Nathan-Busse-private/S.P.A.R.K/Src/Scripts/Alpha/Alpha/Stable/Models/Leg parts/Coxae/x4/Coxae joint bracket.stl

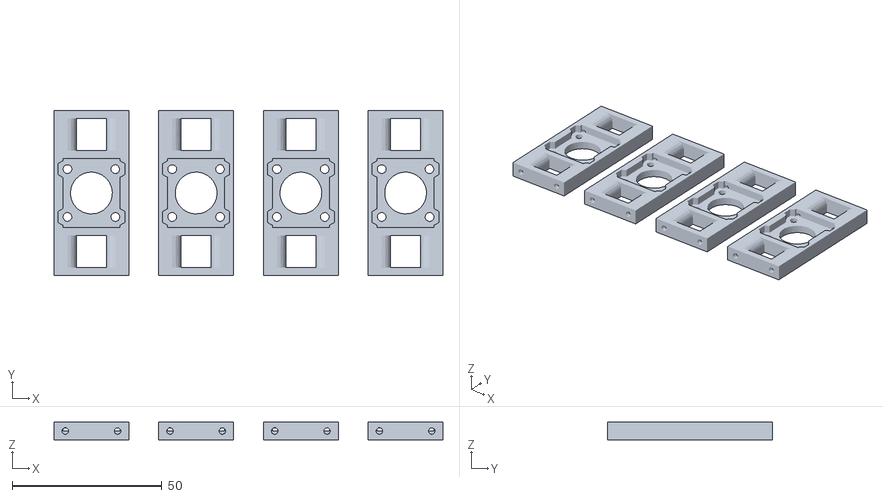
[picture p16: CAD file, 2023-09-16]
Src/Scripts/Alpha/Alpha/Stable/Models/Leg parts/Coxae/x4/Coxae joint bracket.stl
130.0 x 55.2 x 6.00
