Nathan-Busse-private/S.P.A.R.K/Src/Scripts/In-Dev/In-Dev/Stable/Models/Body parts/x1/top.stl

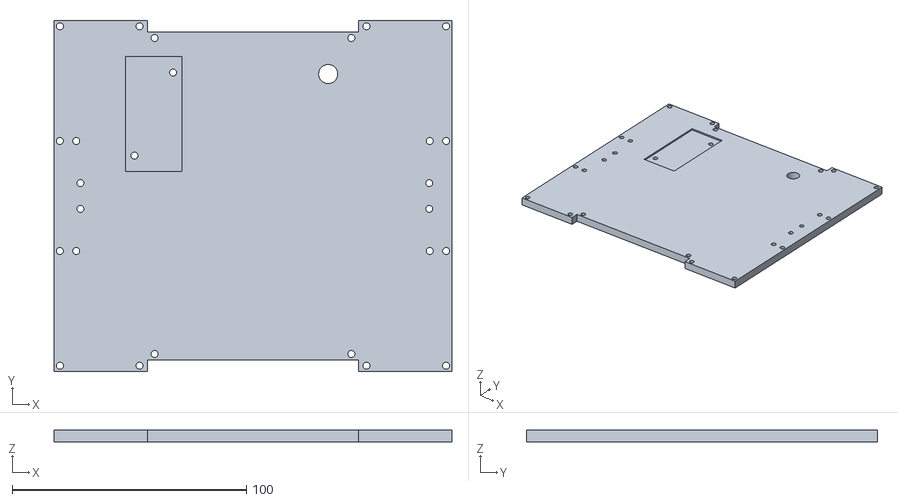
[picture p17: CAD file, 2023-08-11]
Src/Scripts/In-Dev/In-Dev/Stable/Models/Body parts/x1/top.stl
170.0 x 150.0 x 5.00
