Nathan-Busse-private/S.P.A.R.K/Src/Scripts/Alpha/Alpha/Models/Body parts/x1/30mm fan mount.stl

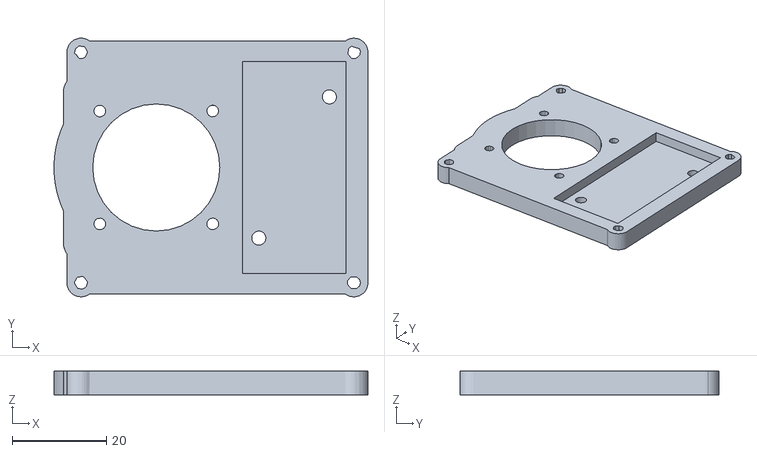
[picture p18: CAD file, 2023-08-11]
Src/Scripts/Alpha/Alpha/Models/Body parts/x1/30mm fan mount.stl
66.7 x 55.0 x 5.00
