Nathan-Busse-private/S.P.A.R.K/Src/Scripts/Alpha/Alpha/Models/Leg parts/Coxae/x4/Coxae joint horn bracket.stl

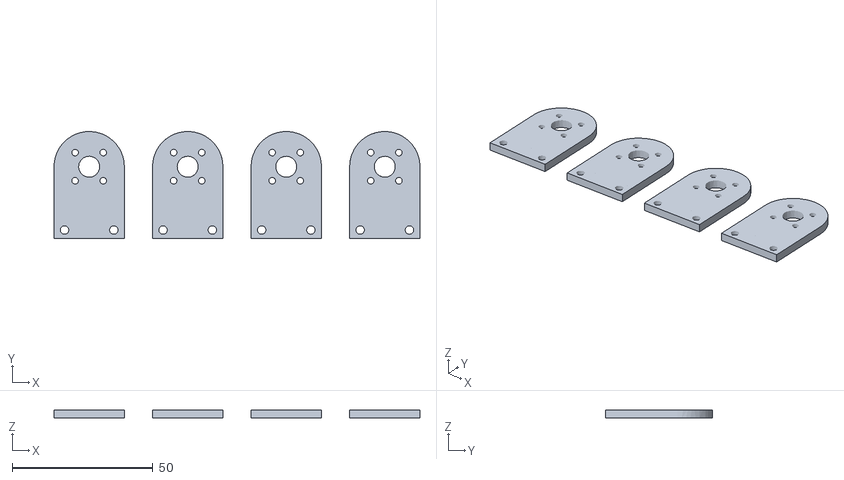
[picture p19: CAD file, 2023-09-16]
Src/Scripts/Alpha/Alpha/Models/Leg parts/Coxae/x4/Coxae joint horn bracket.stl
130.0 x 38.0 x 3.00
