Nathan-Busse-private/S.P.A.R.K/Src/Scripts/Alpha/Alpha/Models/Leg parts/Femur/x1/Femur.stl

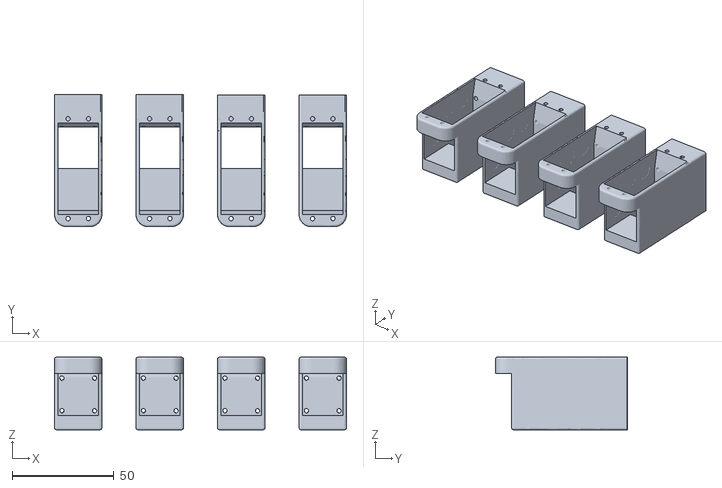
[picture p20: CAD file, 2023-06-04]
Src/Scripts/Alpha/Alpha/Models/Leg parts/Femur/x1/Femur.stl
143.3 x 65.0 x 35.7
