Nathan-Busse-private/S.P.A.R.K/Src/Scripts/Alpha/Alpha/Nightly/Models/Body parts/x1/Battery base panel v3.0.stl

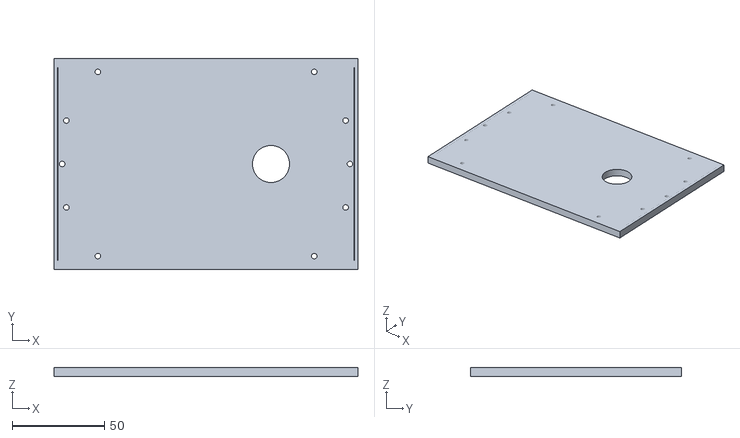
[picture p22: CAD file, 2023-09-16]
Src/Scripts/Alpha/Alpha/Nightly/Models/Body parts/x1/Battery base panel v3.0.stl
164.4 x 114.2 x 5.00
