Nathan-Busse-private/S.P.A.R.K/Src/Scripts/Alpha/Alpha/Nightly/Models/Leg parts/Redesign/Horn.stl

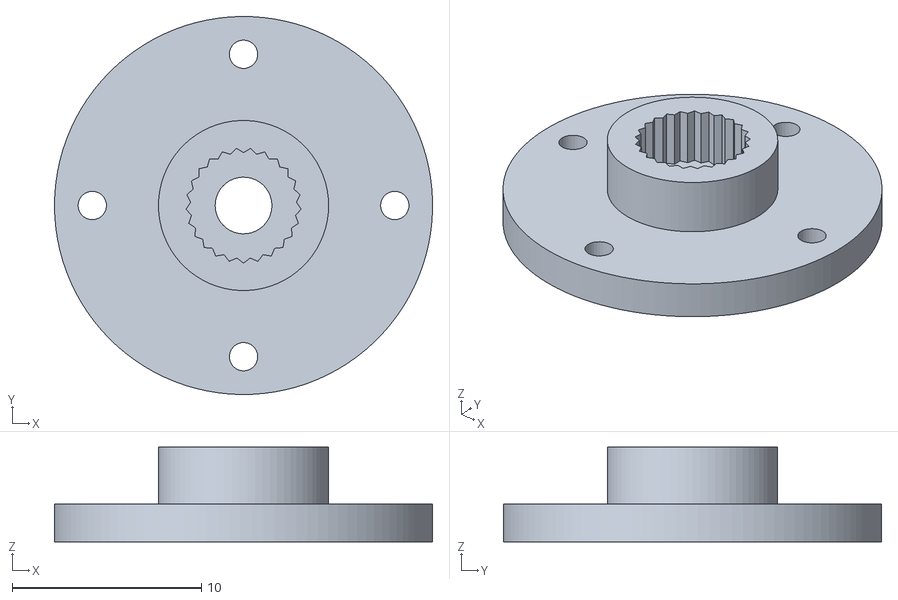
[picture p23: CAD file, 2023-10-25]
Src/Scripts/Alpha/Alpha/Nightly/Models/Leg parts/Redesign/Horn.stl
20.0 x 20.0 x 5.00
