Nathan-Busse-private/S.P.A.R.K/Src/Scripts/Beta/Beta/Models/Leg parts/Tibia/x1/Tibia extension v1.stl

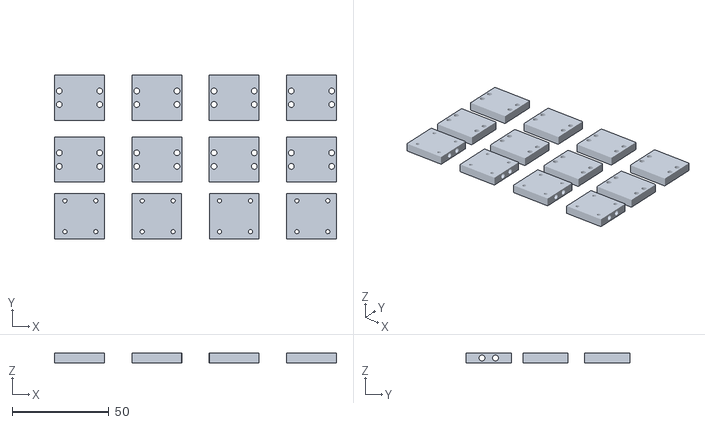
[picture p24: CAD file, 2023-07-13]
Src/Scripts/Beta/Beta/Models/Leg parts/Tibia/x1/Tibia extension v1.stl
145.9 x 84.6 x 5.00
