Nathan-Busse-private/S.P.A.R.K/Src/Scripts/In-Dev/In-Dev/Models/Leg parts/Tibia/x1/Paw v4.stl

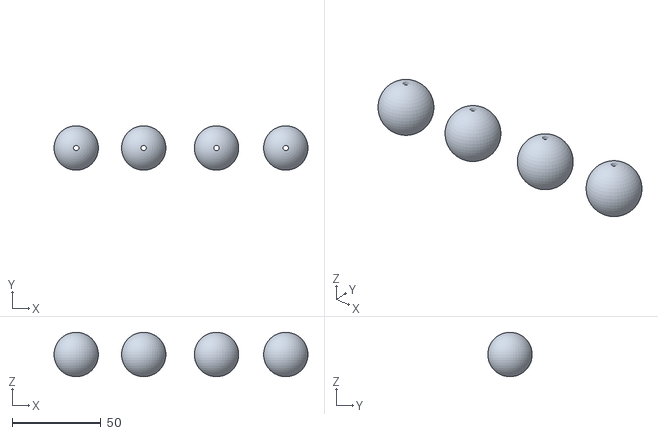
[picture p25: CAD file, 2023-07-13]
Src/Scripts/In-Dev/In-Dev/Models/Leg parts/Tibia/x1/Paw v4.stl
143.0 x 25.0 x 24.8
