Nathan-Busse-private/S.P.A.R.K/Src/Scripts/In-Dev/In-Dev/Nightly/Models/Leg parts/Coxae/x4/Leg Joint bearing v2.stl

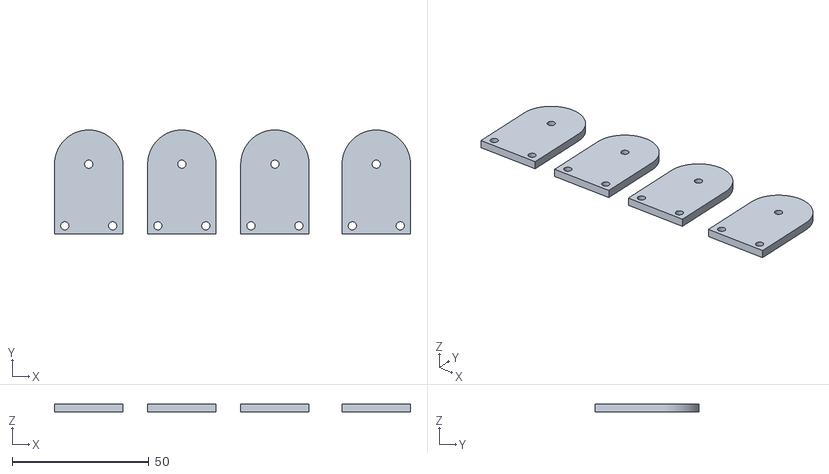
[picture p26: CAD file, 2023-10-25]
Src/Scripts/In-Dev/In-Dev/Nightly/Models/Leg parts/Coxae/x4/Leg Joint bearing v2.stl
130.0 x 38.0 x 3.00
