Nathan-Busse-private/S.P.A.R.K/Src/Scripts/In-Dev/In-Dev/Nightly/Models/Leg parts/Redesign/Tibia v2.stl

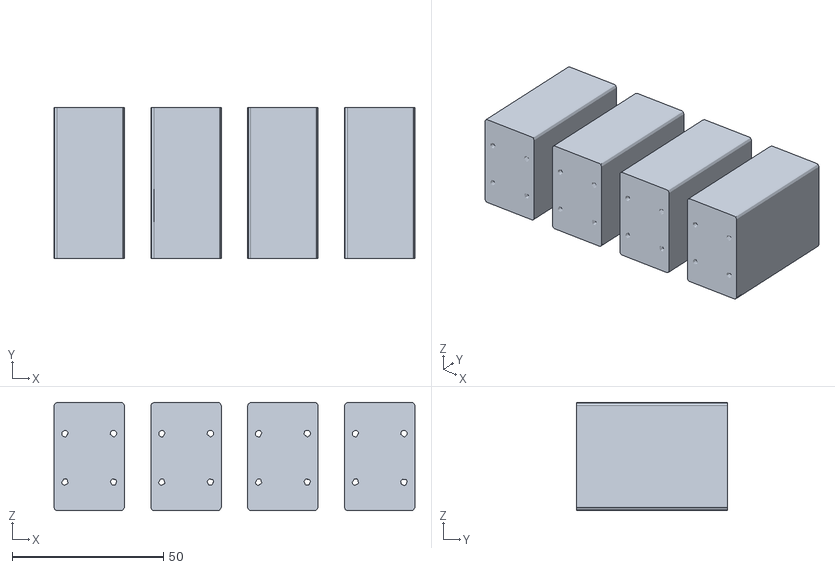
[picture p27: CAD file, 2023-10-25]
Src/Scripts/In-Dev/In-Dev/Nightly/Models/Leg parts/Redesign/Tibia v2.stl
119.3 x 50.0 x 35.7
