Nathan-Busse-private/S.P.A.R.K/Src/Scripts/Alpha/Alpha/Models/Leg parts/Tibia/x1/Tibia joint bearing axel bracket v1.stl

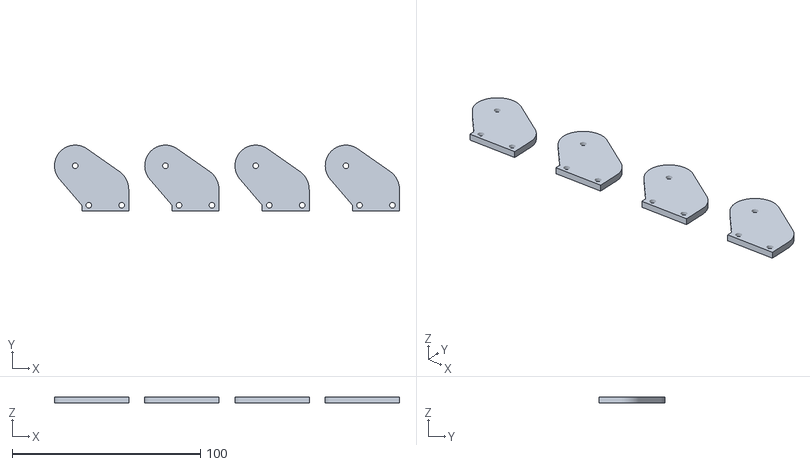
[picture p28: CAD file, 2023-07-13]
Src/Scripts/Alpha/Alpha/Models/Leg parts/Tibia/x1/Tibia joint bearing axel bracket v1.stl
183.5 x 35.0 x 3.00
