Nathan-Busse-private/S.P.A.R.K/Src/Scripts/Alpha/Alpha/Models/Leg parts/Coxae/x4/Coxae.stl

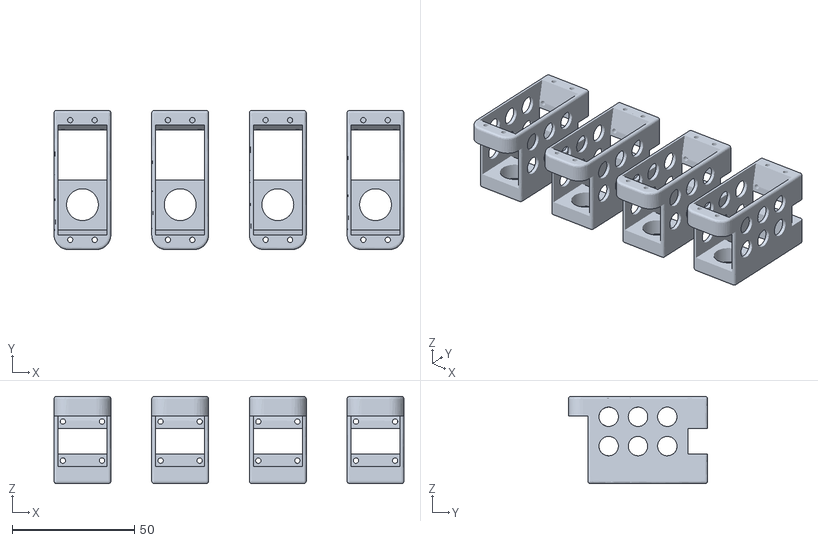
[picture p29: CAD file, 2023-05-07]
Src/Scripts/Alpha/Alpha/Models/Leg parts/Coxae/x4/Coxae.stl
143.3 x 57.0 x 35.7
