Nathan-Busse-private/S.P.A.R.K/Src/Scripts/Alpha/Alpha/Nightly/Models/Leg parts/Redesign/Femur v2.stl

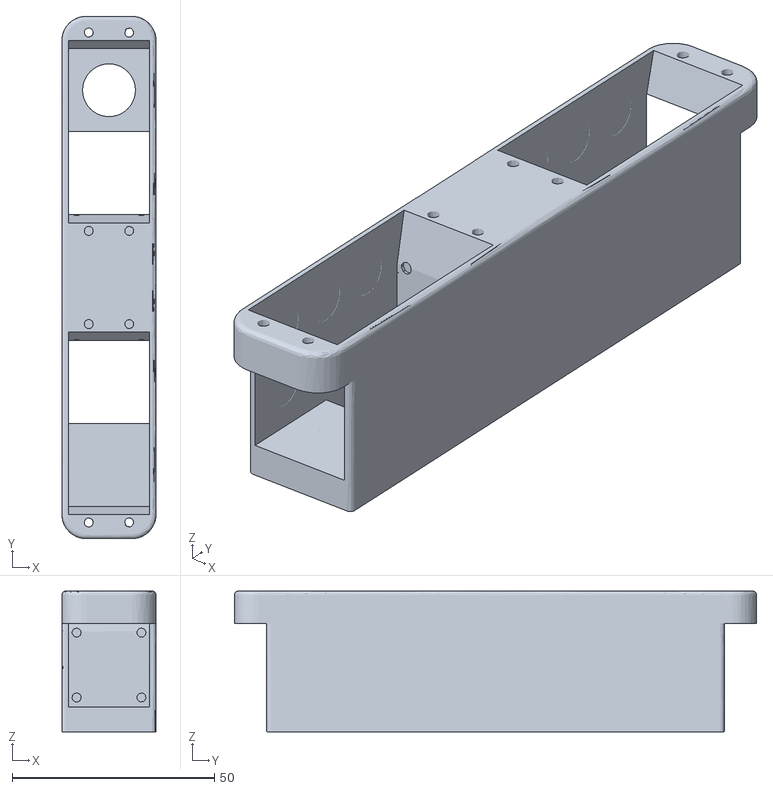
[picture p31: CAD file, 2023-10-20]
Src/Scripts/Alpha/Alpha/Nightly/Models/Leg parts/Redesign/Femur v2.stl
23.3 x 129.0 x 34.8
