Nathan-Busse-private/S.P.A.R.K/Src/Scripts/Alpha/Alpha/Stable/Models/Body parts/x1/Gyro mount.stl

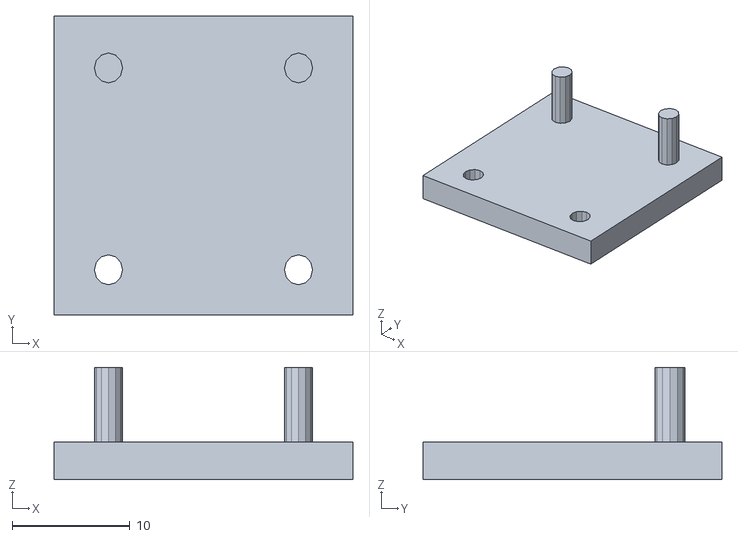
[picture p32: CAD file, 2023-07-24]
Src/Scripts/Alpha/Alpha/Stable/Models/Body parts/x1/Gyro mount.stl
25.4 x 25.4 x 9.52
