Nathan-Busse-private/S.P.A.R.K/Src/Scripts/Beta/Beta/Models/Leg parts/Coxae/x4/Coxae joint end cap.stl

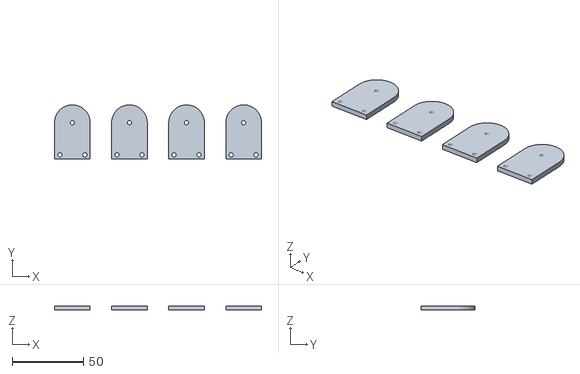
[picture p33: CAD file, 2023-05-07]
Src/Scripts/Beta/Beta/Models/Leg parts/Coxae/x4/Coxae joint end cap.stl
145.0 x 38.0 x 3.00
