Nathan-Busse-private/S.P.A.R.K/Src/Scripts/In-Dev/In-Dev/Stable/Models/Body parts/x1/Battery base panel.stl

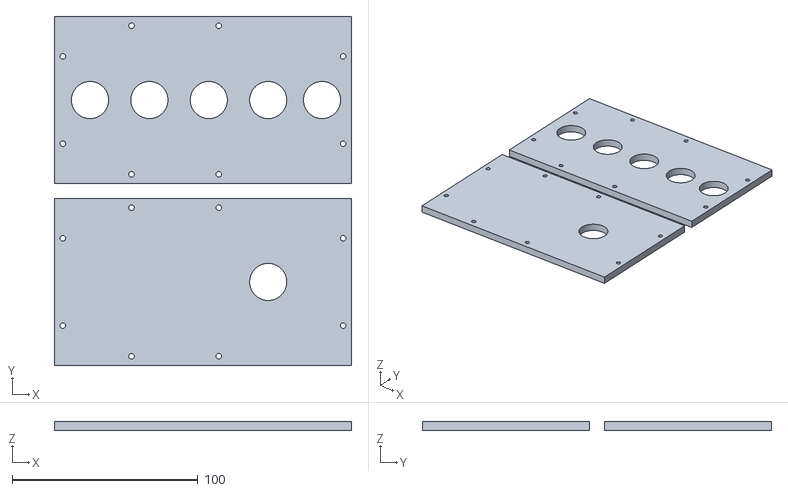
[picture p34: CAD file, 2023-07-24]
Src/Scripts/In-Dev/In-Dev/Stable/Models/Body parts/x1/Battery base panel.stl
160.0 x 188.1 x 5.00
