Nathan-Busse-private/S.P.A.R.K/Src/Scripts/Alpha/Alpha/Stable/Models/Body parts/x1/Battery side wall.stl

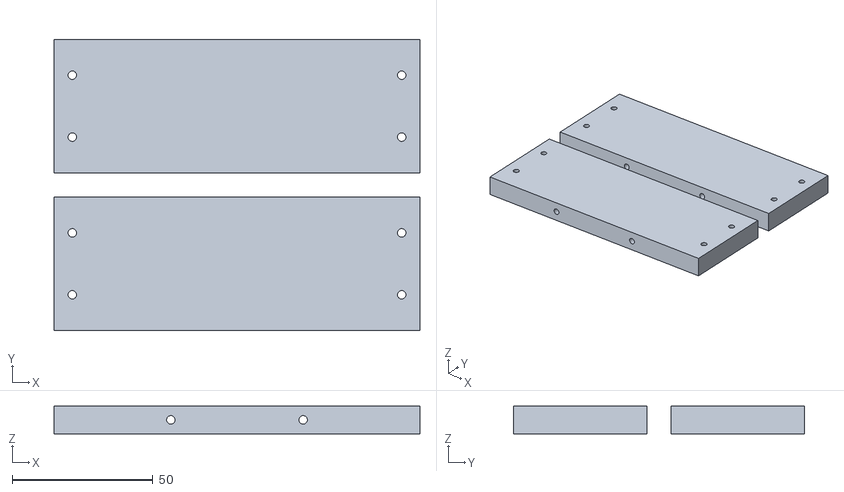
[picture p35: CAD file, 2023-07-24]
Src/Scripts/Alpha/Alpha/Stable/Models/Body parts/x1/Battery side wall.stl
130.0 x 103.3 x 9.90
