Nathan-Busse-private/S.P.A.R.K/Src/Scripts/Alpha/Alpha/Stable/Models/Body parts/x1/GoPro body attachment.stl

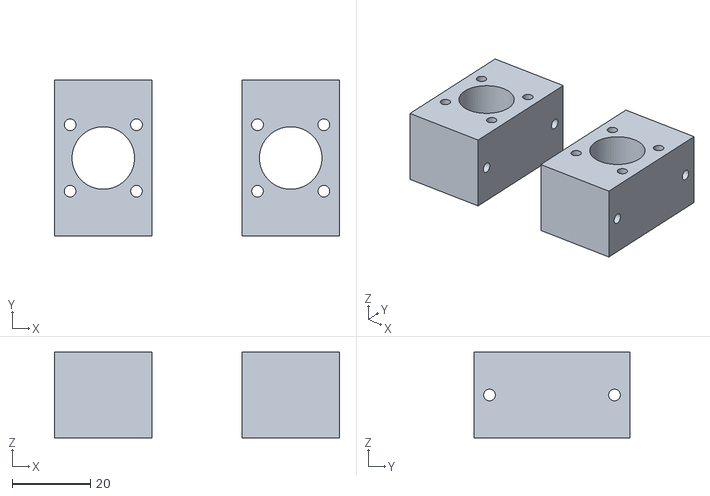
[picture p36: CAD file, 2023-06-17]
Src/Scripts/Alpha/Alpha/Stable/Models/Body parts/x1/GoPro body attachment.stl
73.0 x 40.0 x 22.0
