Nathan-Busse-private/S.P.A.R.K/S.P.A.R.K/Scripts/Tests and development/Tests/Stand_up_test/Stand_up_test.ino

/*
Stand_up test

Project: S.P.A.R.K
Start date: 10 April 2023
Last edited: 20 April 2023
Info:

S.P.A.R.K will perform a series of transitoms from its standing position and returning back to its resting position.
The perpose of this test is to see if the MG996R servos can support the weight of the robot.

Made by Nathan-Busse
*/


// Libraries
#include <Adafruit_PWMServoDriver.h>

// Pin declarations
#define Coxae_A 0
#define Femur_A 1
#define Tibia_A 2

#define Coxae_B 4
#define Femur_B 5
#define Tibia_B 6

#define Coxae_C 8
#define Femur_C 9
#define Tibia_C 10

#define Coxae_D 12
#define Femur_D 13
#define Tibia_D 14

// Degree declarations
// Resting position
#define C_idle 90
#define F_rest_L 180
#define F_rest_R 0
#define T_rest 0

// Standing position
#define C_idle 90
#define F_stand_L 135
#define F_stand_R 45
#define T_stand 45

// Define time delay
#define hold 100

// PWM setup
#define MIN_PulseLength 500
#define MAX_PulseLength 2500
#define MED_PulseLength 2500
#define Frequency 50  // 50 HRz

Adafruit_PWMServoDriver pwm = Adafruit_PWMServoDriver();
int degrees;

void setup() {

  pwm.begin();
  pwm.setPWMFreq(Frequency);
}

void loop() {
  // Rest postion
  pwm.setPWM(Coxae_A, 0, pulseWidth(C_idle));
  pwm.setPWM(Coxae_B, 0, pulseWidth(C_idle));
  pwm.setPWM(Coxae_C, 0, pulseWidth(C_idle));
  pwm.setPWM(Coxae_D, 0, pulseWidth(C_idle));

  pwm.setPWM(Femur_A, 0, pulseWidth(F_rest_L));
  pwm.setPWM(Femur_B, 0, pulseWidth(F_rest_L));
  pwm.setPWM(Femur_C, 0, pulseWidth(F_rest_R));
  pwm.setPWM(Femur_D, 0, pulseWidth(F_rest_R));

  pwm.setPWM(Tibia_A, 0, pulseWidth(T_rest));
  pwm.setPWM(Tibia_B, 0, pulseWidth(T_rest));
  pwm.setPWM(Tibia_C, 0, pulseWidth(T_rest));
  pwm.setPWM(Tibia_D, 0, pulseWidth(T_rest));

  delay(hold);

  // Stand position
  pwm.setPWM(Coxae_A, 0, pulseWidth(C_idle));
  pwm.setPWM(Coxae_B, 0, pulseWidth(C_idle));
  pwm.setPWM(Coxae_C, 0, pulseWidth(C_idle));
  pwm.setPWM(Coxae_D, 0, pulseWidth(C_idle));

  pwm.setPWM(Femur_A, 0, pulseWidth(F_stand_L));
  pwm.setPWM(Femur_B, 0, pulseWidth(F_stand_L));
  pwm.setPWM(Femur_C, 0, pulseWidth(F_stand_R));
  pwm.setPWM(Femur_D, 0, pulseWidth(F_stand_R));

  pwm.setPWM(Tibia_A, 0, pulseWidth(T_stand));
  pwm.setPWM(Tibia_B, 0, pulseWidth(T_stand));
  pwm.setPWM(Tibia_C, 0, pulseWidth(T_stand));
  pwm.setPWM(Tibia_D, 0, pulseWidth(T_stand));
}

// Pulsewidth declaration
int pulseWidth(int angle) {
  int pulse_wide, analog_value;
  pulse_wide = map(angle, 0, 180, MIN_PulseLength, MAX_PulseLength);
  analog_value = int(float(pulse_wide) / 1000000 * Frequency * 4096);
  Serial.println(analog_value);
  return analog_value;
}
