Nathan-Busse-private/S.P.A.R.K/Src/Scripts/Alpha/Alpha/Nightly/Scripts/Python/Simulation/Scripts/Package_install.py

import os
import sys


print('\033[2;32;43m Installing python packages...')	

os.system('cmd /c "pip install pybullet"')


dirname = os.path.dirname("Server")
file_path = 'c:/users/' + os.getlogin()
filename = os.path.join(dirname, file_path,'./Documents/My Bedrock Server/MCBE Server/Server' )

os.mkdir(filename)

# mode
mode = 0o666
  
# Path
path = os.path.join(filename)
  
print("Directory '% s' created" )

sys.exit()
